bowie-dev/Sim-Racing-Handbrake/img/1.png

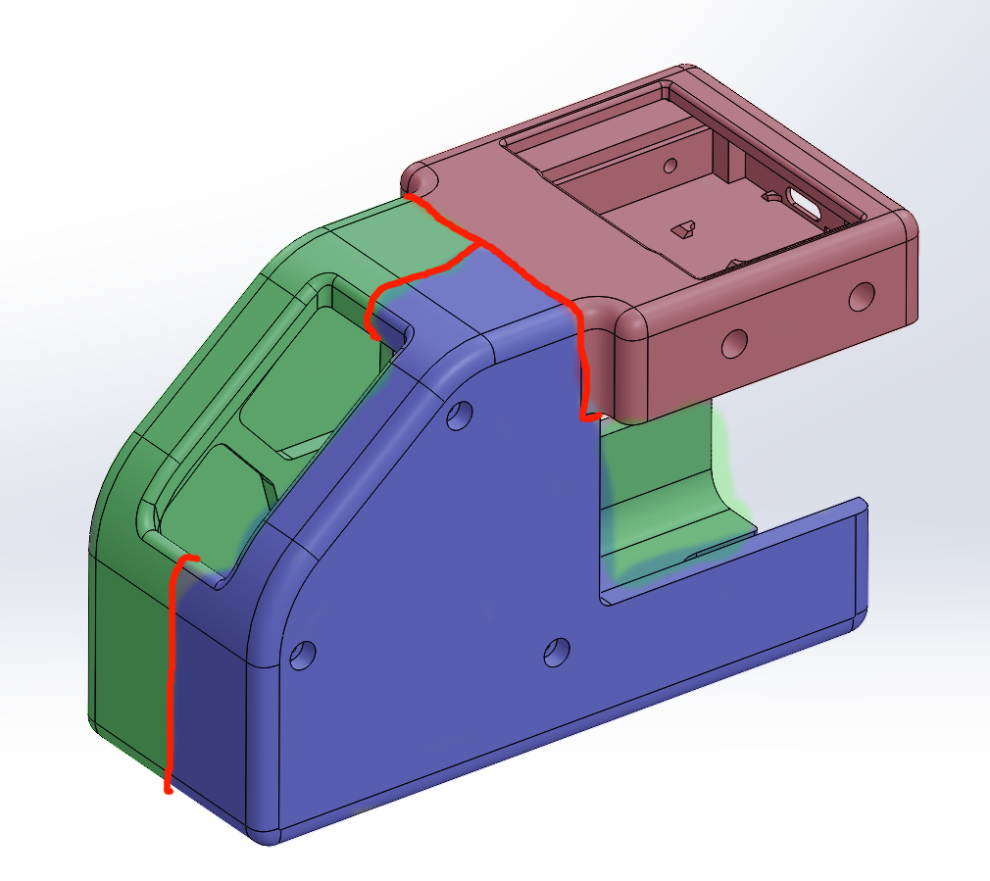
img/1.png
