bowie-dev/Sim-Racing-Handbrake/img/2.png

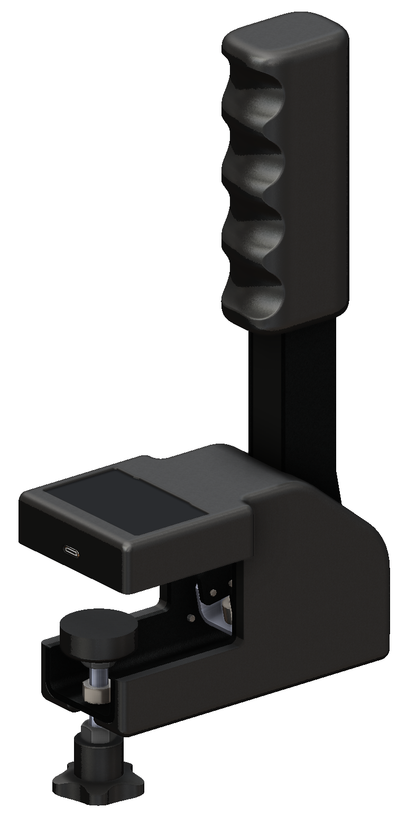
img/2.png
