bowie-dev/Sim-Racing-Handbrake/img/3.png

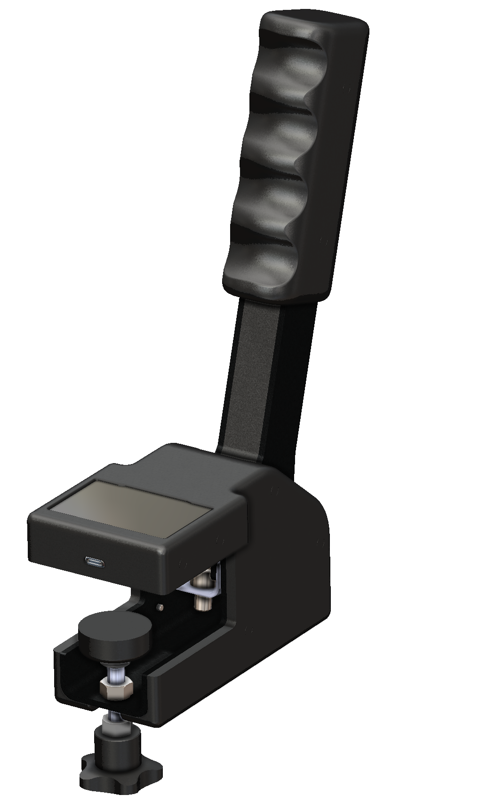
img/3.png
