bowie-dev/Sim-Racing-Handbrake/img/4.png

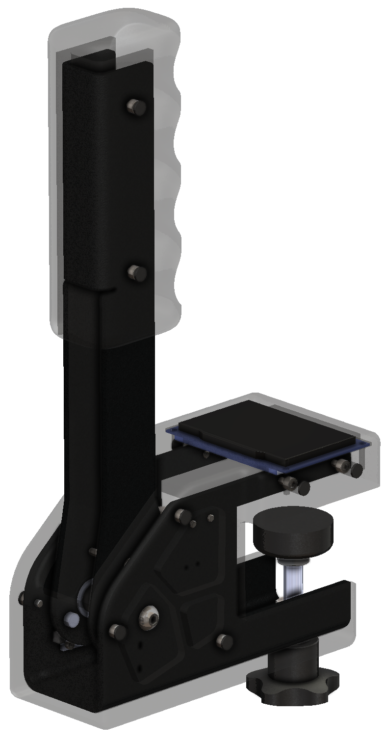
img/4.png
