bowie-dev/Sim-Racing-Handbrake/img/dynamic.png

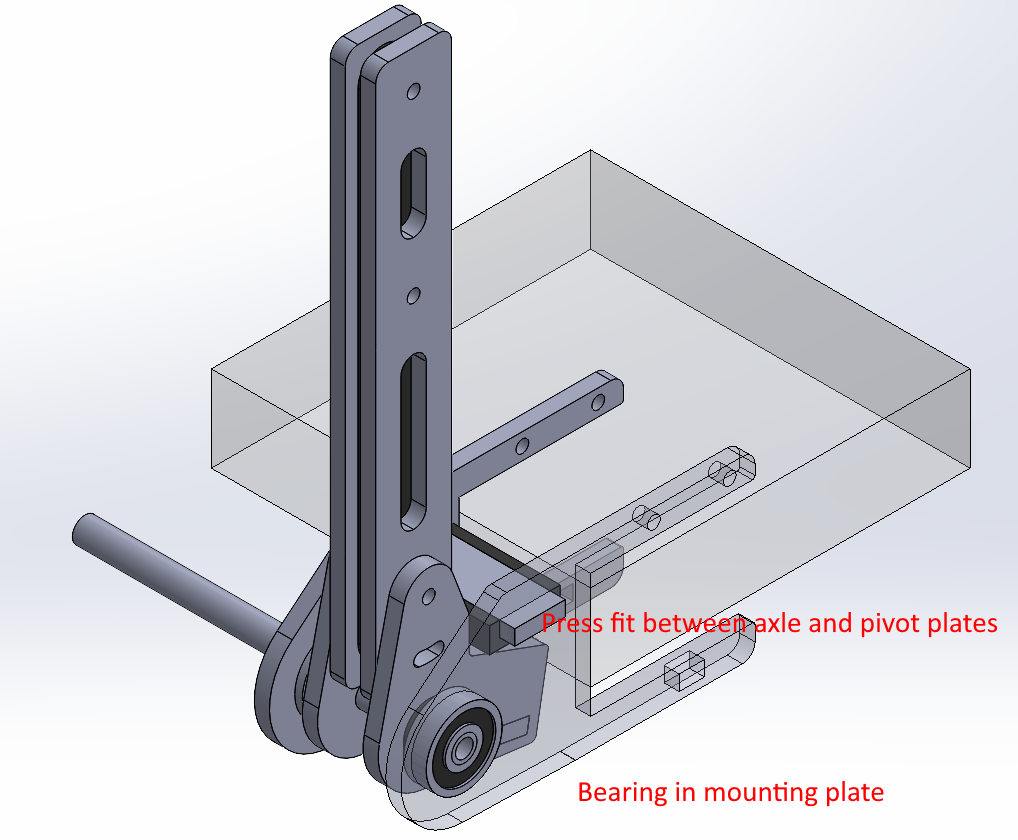
img/dynamic.png
