bowie-dev/Sim-Racing-Handbrake/CAD/STEP Files/shaft spacer side.STEP

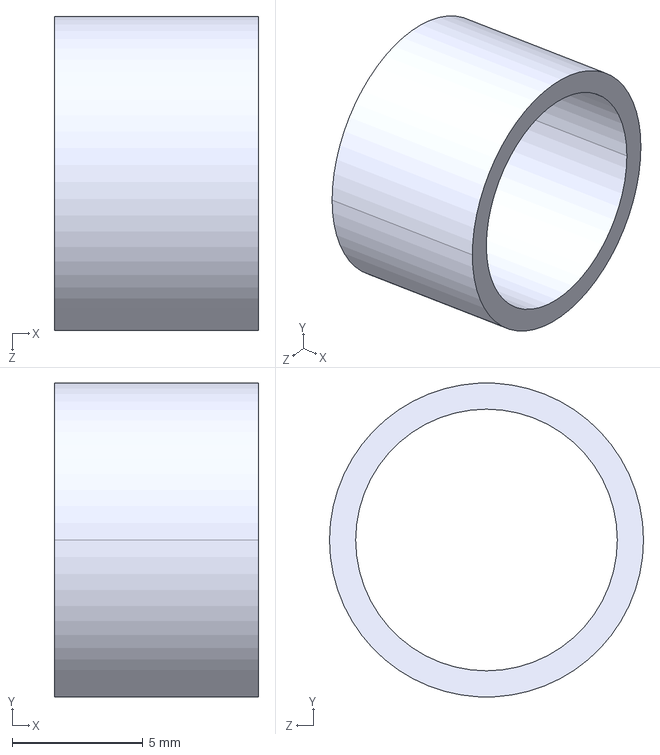
[picture p27: CAD file, 2026-06-10]
CAD/STEP Files/shaft spacer side.STEP
7.80 x 12.0 x 12.0 mm
