bowie-dev/Sim-Racing-Handbrake/CAD/STEP Files/RP2040.STEP

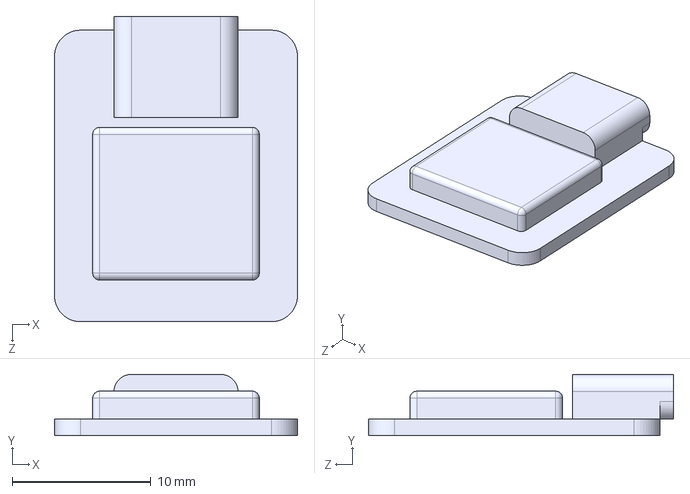
[picture p28: CAD file, 2026-06-10]
CAD/STEP Files/RP2040.STEP
17.5 x 4.41 x 22.0 mm
