bowie-dev/Sim-Racing-Handbrake/CAD/STEP Files/magnet.STEP

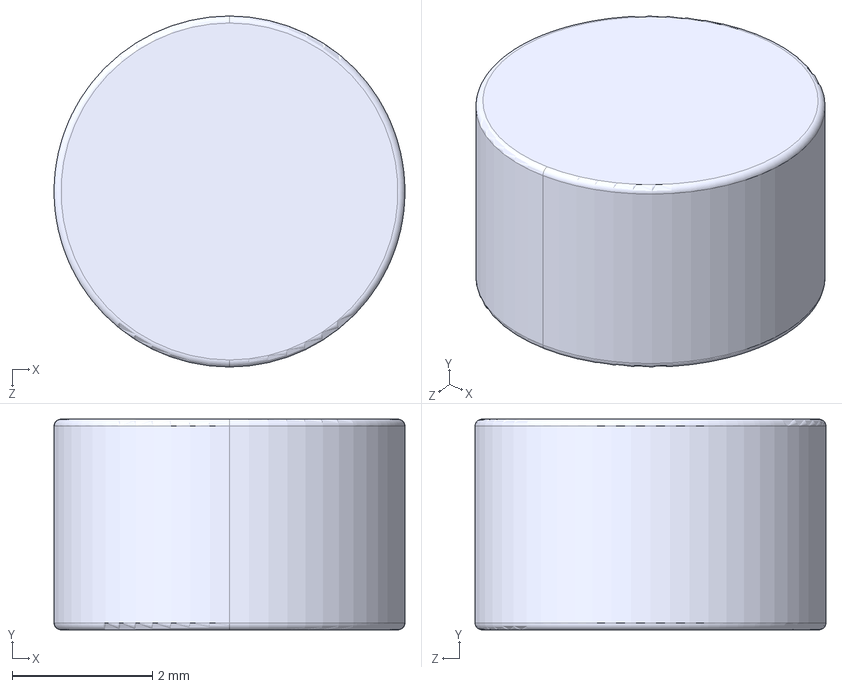
[picture p29: CAD file, 2026-06-10]
CAD/STEP Files/magnet.STEP
5.00 x 3.00 x 5.00 mm
