bowie-dev/Sim-Racing-Handbrake/CAD/STEP Files/m3 insert.STEP

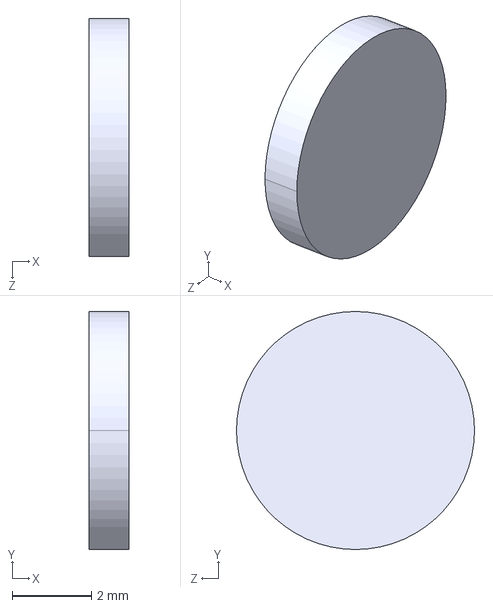
[picture p30: CAD file, 2026-06-10]
CAD/STEP Files/m3 insert.STEP
1.00 x 6.00 x 6.00 mm
