bowie-dev/Sim-Racing-Handbrake/CAD/SOLIDWORKS/assembly.SLDASM

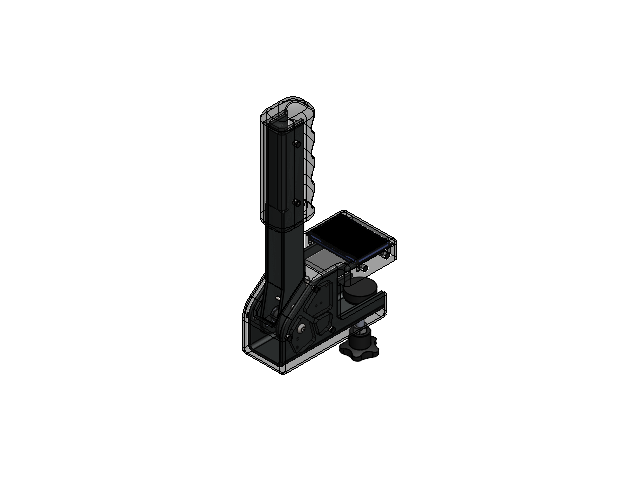
[picture p31: CAD file, 2026-06-10]
CAD/SOLIDWORKS/assembly.SLDASM
bearing x 2
cylinder magnet
grip
hall effect
lcd
microswitch
mount dynamic sheet metal bwend
pivot dynamic two part bent
shaft spacer
spring plate x 2
shaft
shaft spacer sides x 2
case clean
rp2040n
螺杆^DADJ-D33-M8-L50
螺母^DADJ-D33-M8-L50
底座^DADJ-D33-M8-L50
DBTJ-W-D40-M8
socket head cap screw_iso x 28
socket button head screw_iso x 4
hex nut style 1 gradeab_iso x 4
m3 insert x 14
