bowie-dev/Sim-Racing-Handbrake/img/assembly.png

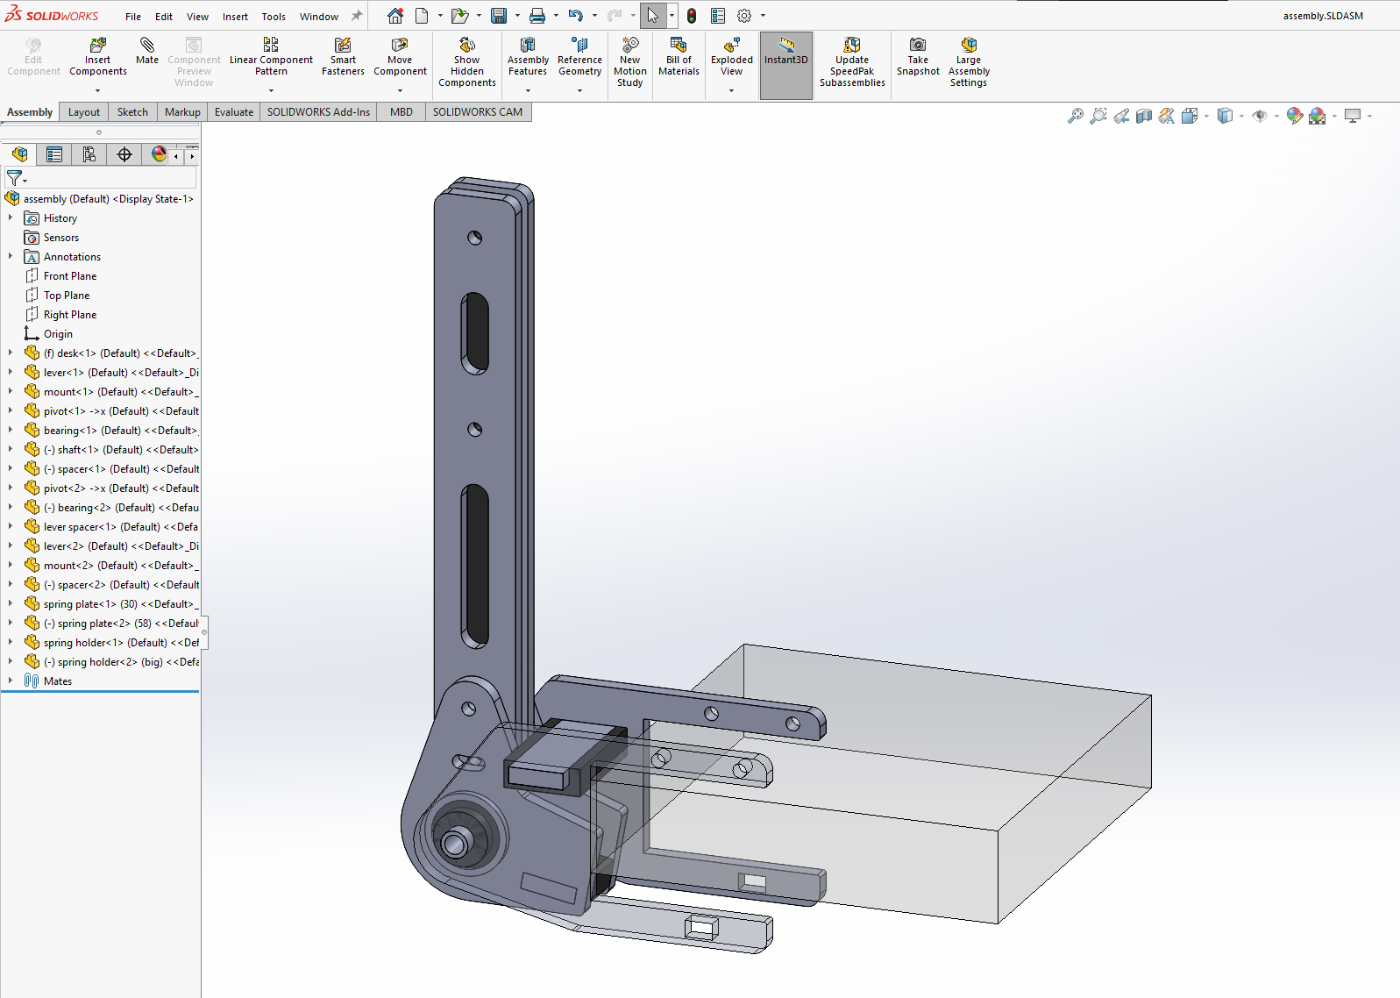
img/assembly.png
